LoyalPotato/yggdrasil/plates/rev1/plates.png

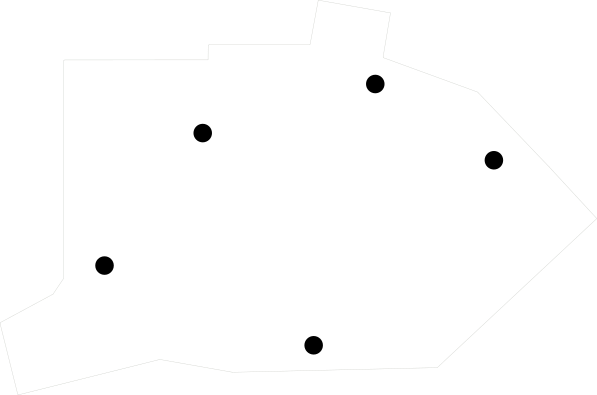
plates/rev1/plates.png
